bythorsthunder/Orion-Tri-Belt/STLs/Z_Bed_Mount_Right.stl

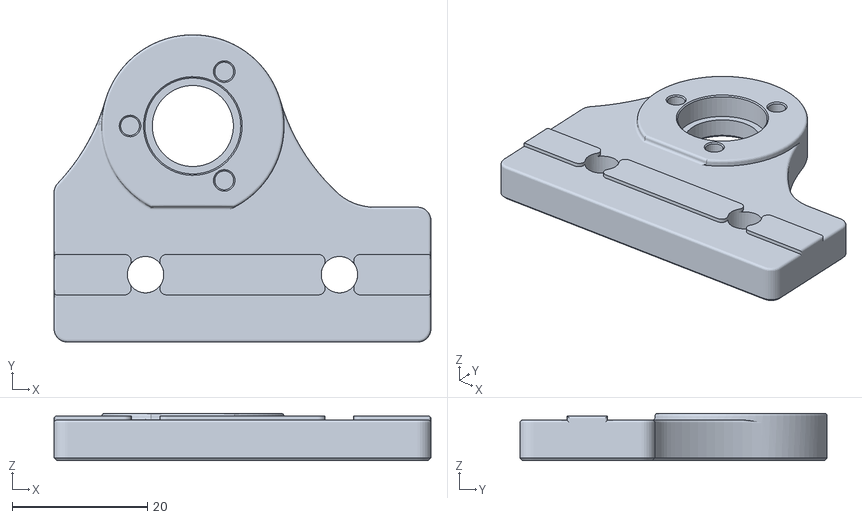
[picture p16: CAD file, 2022-09-08]
STLs/Z_Bed_Mount_Right.stl
55.8 x 45.5 x 7.00
