bythorsthunder/Orion-Tri-Belt/STLs/Z_Carriage_Rear_3Hole.stl

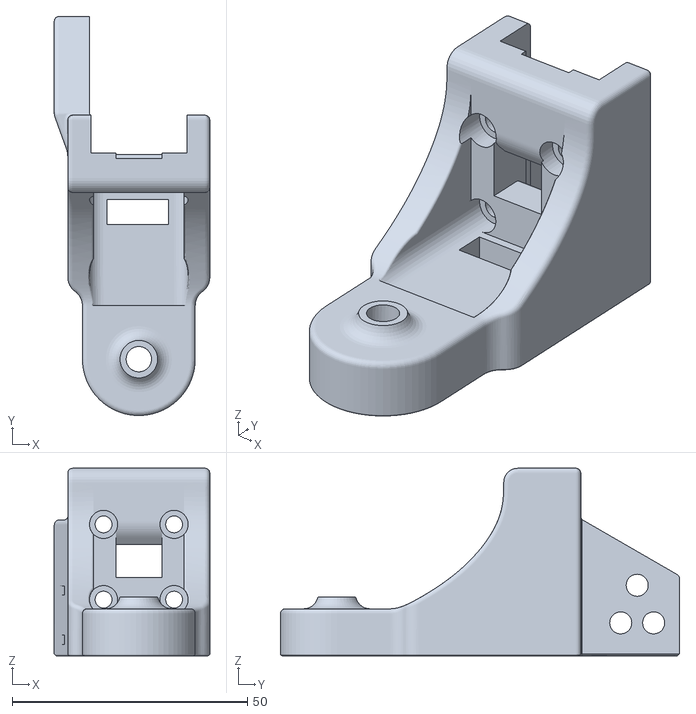
[picture p17: CAD file, 2022-09-08]
STLs/Z_Carriage_Rear_3Hole.stl
33.1 x 84.9 x 39.9
