bythorsthunder/Orion-Tri-Belt/STLs/Z_Drive_Rear_Motor_Mount.stl

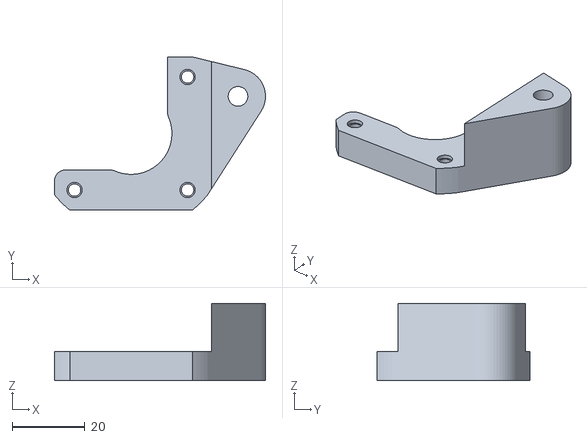
[picture p18: CAD file, 2022-09-08]
STLs/Z_Drive_Rear_Motor_Mount.stl
57.9 x 42.0 x 21.2
