bythorsthunder/Orion-Tri-Belt/STLs/Z_Idler_Rear.stl

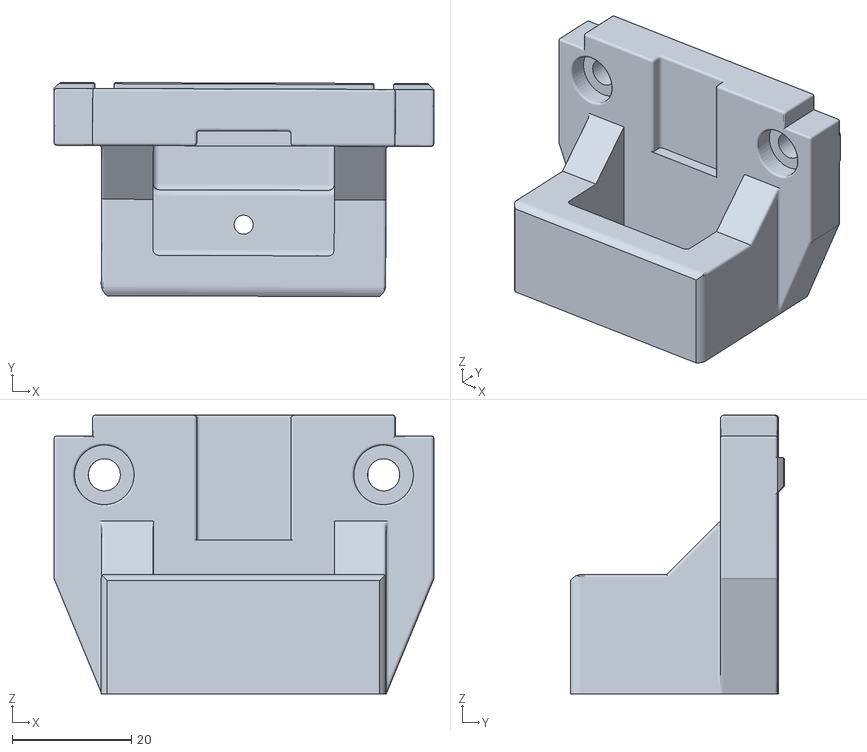
[picture p19: CAD file, 2022-09-08]
STLs/Z_Idler_Rear.stl
63.7 x 35.9 x 46.7
