bythorsthunder/Orion-Tri-Belt/STLs/Gantry_Stabilizer.stl

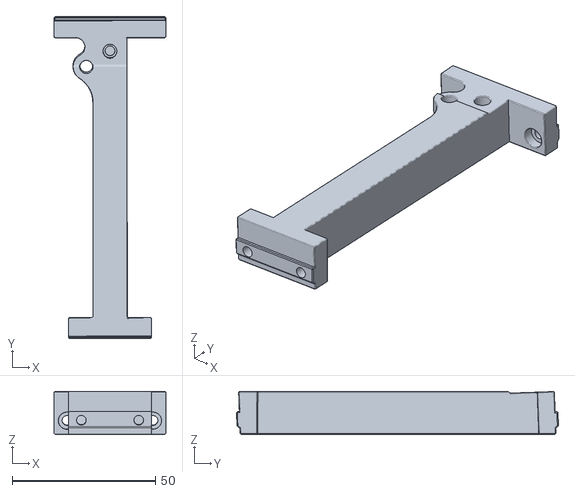
[picture p20: CAD file, 2022-09-08]
STLs/Gantry_Stabilizer.stl
39.0 x 112.2 x 15.0
