bythorsthunder/Orion-Tri-Belt/STLs/[a]_Z_Belt_Clamp_Right.stl

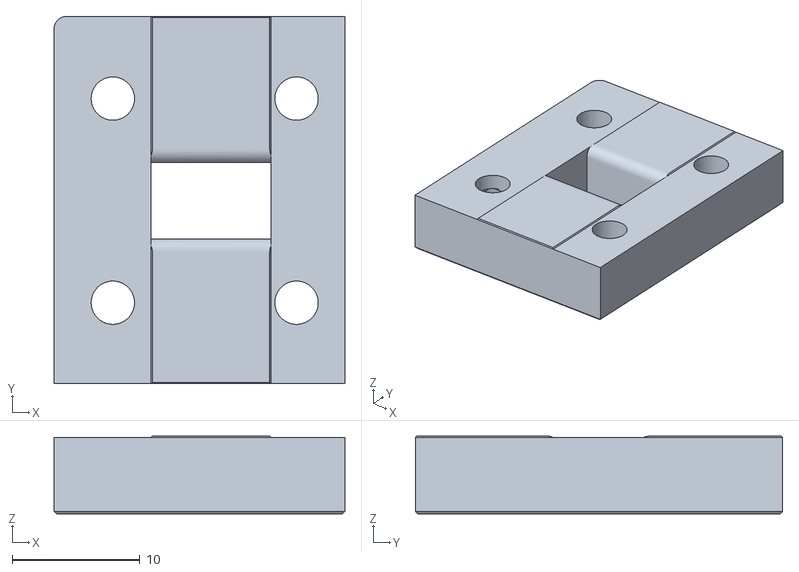
[picture p21: CAD file, 2022-09-08]
STLs/[a]_Z_Belt_Clamp_Right.stl
22.8 x 28.8 x 6.10
