bythorsthunder/Orion-Tri-Belt/STLs/Z_Carriage_Left.stl

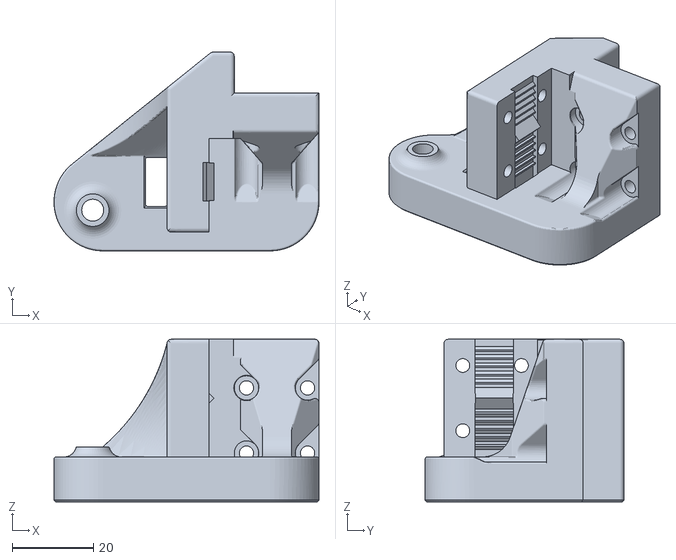
[picture p22: CAD file, 2022-09-08]
STLs/Z_Carriage_Left.stl
65.0 x 48.8 x 39.9
