bythorsthunder/Orion-Tri-Belt/STLs/[a]_Z_Drive_Rear_Loop_Tensioner_Clip.stl

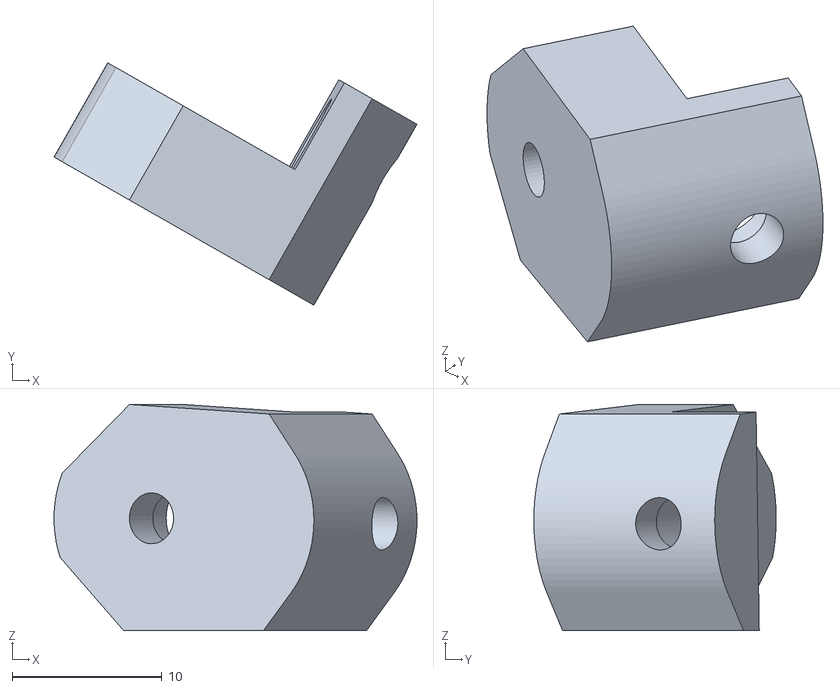
[picture p24: CAD file, 2022-09-08]
STLs/[a]_Z_Drive_Rear_Loop_Tensioner_Clip.stl
24.3 x 16.2 x 15.1
