bythorsthunder/Orion-Tri-Belt/STLs/AB_Idler_Left_Lower.stl

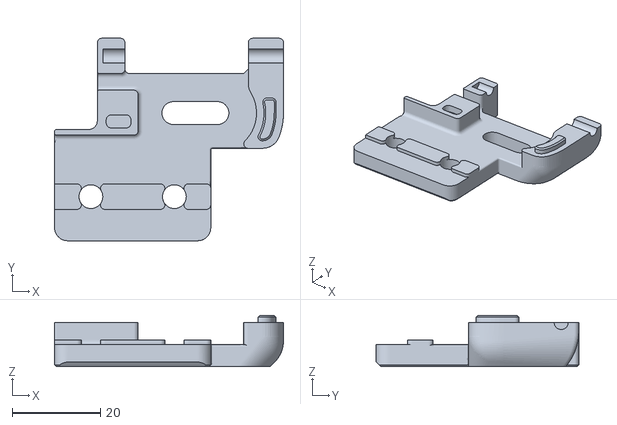
[picture p25: CAD file, 2022-09-08]
STLs/AB_Idler_Left_Lower.stl
52.0 x 46.0 x 11.6
