bythorsthunder/Orion-Tri-Belt/STLs/AB_Idler_Right_Lower.stl

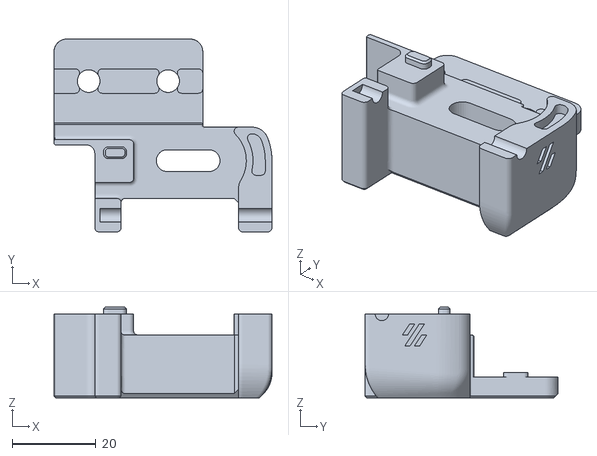
[picture p26: CAD file, 2022-09-08]
STLs/AB_Idler_Right_Lower.stl
52.0 x 46.0 x 21.6
