bythorsthunder/Orion-Tri-Belt/STLs/Z_Drive_Rear_Loop_Tensioner.stl

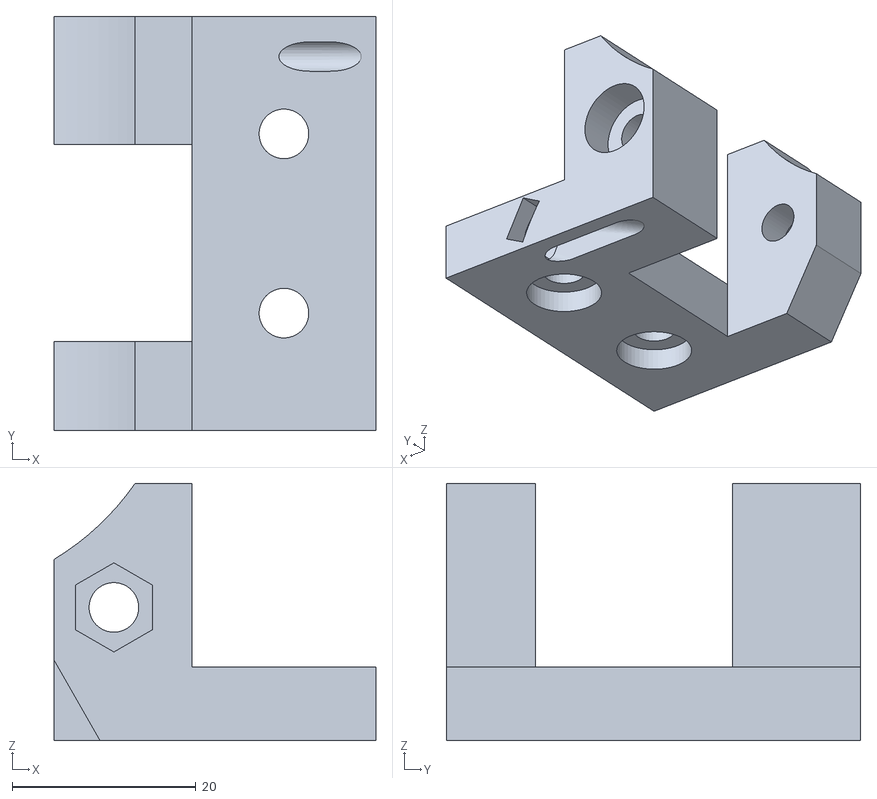
[picture p27: CAD file, 2022-09-08]
STLs/Z_Drive_Rear_Loop_Tensioner.stl
35.0 x 45.0 x 28.0
