bythorsthunder/Orion-Tri-Belt/STLs/Z_Drive_Rear_Retainer.stl

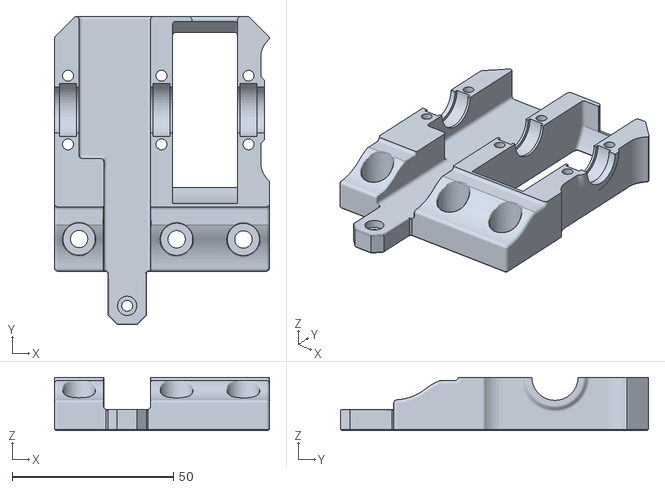
[picture p28: CAD file, 2022-09-08]
STLs/Z_Drive_Rear_Retainer.stl
66.7 x 95.5 x 16.6
